circlesmiler/iwork/src/Icons.h

#include <Particle.h>

/*
 * Icons must have a pixel size that can be devided by 8!
 * Created by http://javl.github.io/image2cpp/
 */
const unsigned char drehpunktIcon[] PROGMEM = {
  0x00, 0x00, 0x00, 0x00, 0x00, 0x00, 0x00, 0x00, 0x00, 0x00, 0x00, 0x00, 0x00, 0x00, 0x00, 0x80,
  0x00, 0x00, 0x00, 0x00, 0x01, 0x80, 0x00, 0x00, 0x00, 0x00, 0x03, 0x80, 0x00, 0x00, 0x00, 0x00,
  0x07, 0x00, 0x00, 0x00, 0x00, 0x00, 0x0f, 0x00, 0x00, 0x00, 0x00, 0x00, 0x1f, 0x00, 0x00, 0x00,
  0x00, 0x00, 0x1f, 0x00, 0x00, 0x00, 0x00, 0x00, 0x00, 0x00, 0x00, 0x00, 0x00, 0x00, 0x00, 0x00,
  0x00, 0x00, 0x00, 0x00, 0x00, 0x00, 0x00, 0x00, 0x00, 0x00, 0x00, 0x18, 0x00, 0x00, 0x00, 0x00,
  0x00, 0x1f, 0x00, 0x00, 0x00, 0x00, 0x00, 0x1f, 0x80, 0x00, 0x00, 0x00, 0x00, 0x1f, 0x80, 0x00,
  0x00, 0x00, 0x00, 0x1f, 0x86, 0x00, 0x00, 0x00, 0x3e, 0x1f, 0x87, 0x00, 0x00, 0x00, 0x3f, 0xc7,
  0x87, 0x80, 0x00, 0x00, 0x3f, 0xc0, 0x07, 0xe0, 0x00, 0x00, 0x7f, 0xc0, 0x07, 0xf0, 0x00, 0x00,
  0x7f, 0xc6, 0x07, 0xf0, 0x00, 0x00, 0x7f, 0xc7, 0x80, 0x38, 0x00, 0x00, 0x7f, 0xc7, 0x80, 0x00,
  0x00, 0x00, 0x7f, 0x8f, 0x80, 0x00, 0x00, 0x00, 0x3f, 0x8f, 0x80, 0x00, 0x03, 0xc0, 0x01, 0x0f,
  0x80, 0x00, 0x01, 0xfc, 0x00, 0x0f, 0x00, 0x00, 0x00, 0xfc, 0x80, 0x1f, 0x00, 0x00, 0x00, 0x78,
  0xf0, 0x1f, 0x00, 0x00, 0x00, 0x38, 0xfc, 0x1f, 0x00, 0x00, 0x00, 0x18, 0xfc, 0x3f, 0x00, 0x00,
  0x00, 0x00, 0xfc, 0x3e, 0x00, 0x00, 0x00, 0x00, 0xfc, 0x3e, 0x00, 0x00, 0x00, 0x00, 0x7c, 0x7e,
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
	0x90, 0x38, 0x04, 0x60, 0x38, 0x00, 0x00, 0x1c, 0x00, 0x00, 0x06, 0x00, 0x00, 0x03, 0x00, 0x00,
	0x01, 0x80, 0x00, 0x00, 0xc0, 0x00, 0x00, 0x70, 0x00, 0x00, 0x78, 0x00, 0x00, 0x7c, 0x00, 0x01,
	0xff, 0x00, 0x00, 0x00, 0x00, 0x00, 0x00, 0x00
};
