circlesmiler/iwork/src/WeatherModel.cpp

#include <Particle.h>

#include "WeatherModel.h"

WeatherModel::WeatherModel(int owmCityIdEEPROMAddress) {
  owmCityIdEEPROMAddress_ = owmCityIdEEPROMAddress;
  setCityId(loadCityIdFromEEPROM());
  outdoorTemp_ = 0;
}

void WeatherModel::setOutdoorData(const char *data) {
  outdoorTemp_ = atof(data);
}

int WeatherModel::getCityId() {
  return cityId_;
}

void WeatherModel::setCityId(int cityId) {
  cityId_ = cityId;
  EEPROM.put(owmCityIdEEPROMAddress_, cityId_);
}

int WeatherModel::getOutdoorTemp() {
  return outdoorTemp_;
}

int WeatherModel::loadCityIdFromEEPROM() {
    int cityId;
    EEPROM.get(owmCityIdEEPROMAddress_, cityId);
    if (cityId > 0)
      return cityId;
    else
      return 2844588;
}

void WeatherModel::setIndoorValues(float temperature, float humidity) {
  indoorTemperature_ = temperature;
  indoorHumidity_ = humidity;
}

float WeatherModel::getIndoorTemperature() {
  return indoorTemperature_;
}

float WeatherModel::getIndoorHumidity() {
  return indoorHumidity_;
}
